WJOchman/modular_hpc/research_folder/Images/PXE.jpg

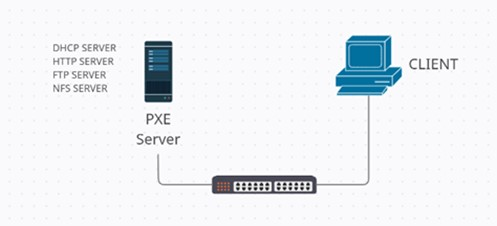
research_folder/Images/PXE.jpg
