WJOchman/modular_hpc/research_folder/Images/squeue.jpeg

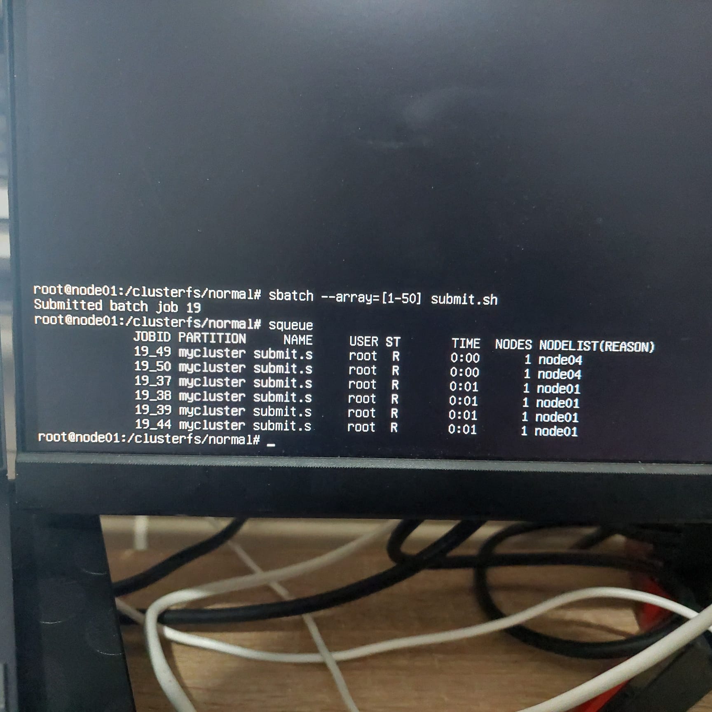
research_folder/Images/squeue.jpeg
