WJOchman/modular_hpc/hpc_case_design/laser_cutting/dxf_files/outer_shelf/outer_layer_b.dxf

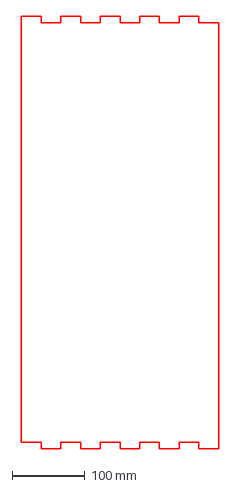
[picture p39: CAD file, 2024-04-06]
hpc_case_design/laser_cutting/dxf_files/outer_shelf/outer_layer_b.dxf
270.0 x 593.0 mm
