WJOchman/modular_hpc/hpc_case_design/3d_printing/stl_files/general-shelf/shelf_handle.stl

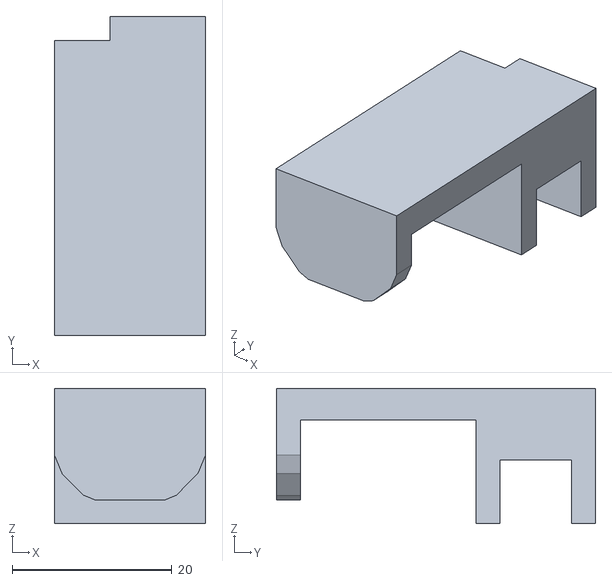
[picture p40: CAD file, 2024-04-06]
hpc_case_design/3d_printing/stl_files/general-shelf/shelf_handle.stl
18.9 x 40.0 x 17.0
