WJOchman/modular_hpc/hpc_case_design/laser_cutting/dxf_files/inner_shelf/inner_shelf_top.dxf

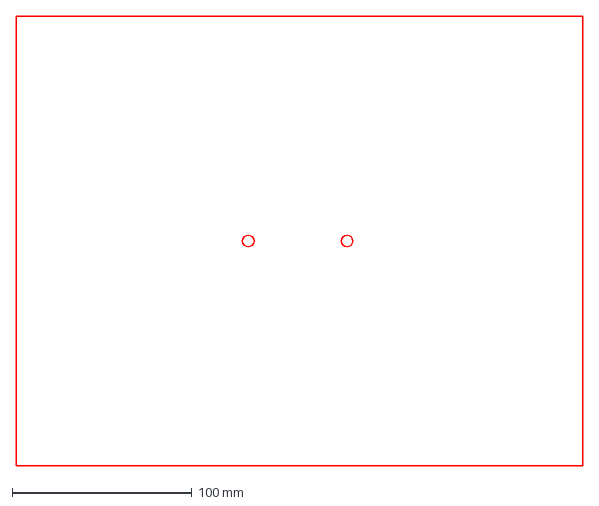
[picture p42: CAD file, 2024-04-06]
hpc_case_design/laser_cutting/dxf_files/inner_shelf/inner_shelf_top.dxf
315.0 x 250.0 mm
