WJOchman/modular_hpc/hpc_case_design/3d_printing/stl_files/general-shelf/truss.stl

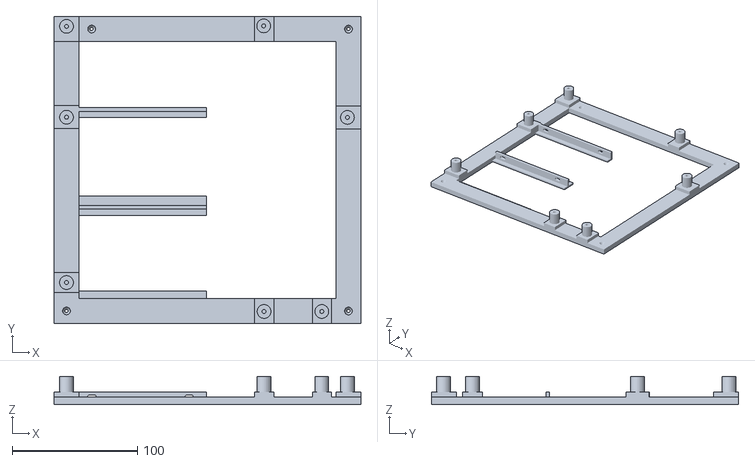
[picture p43: CAD file, 2024-04-06]
hpc_case_design/3d_printing/stl_files/general-shelf/truss.stl
244.8 x 244.8 x 22.4
