WJOchman/modular_hpc/hpc_case_design/laser_cutting/dxf_files/inner_shelf/inner_head_shelf_back.dxf

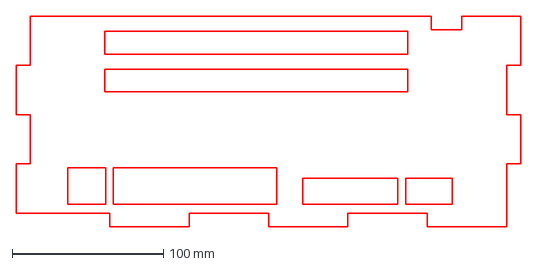
[picture p45: CAD file, 2024-04-06]
hpc_case_design/laser_cutting/dxf_files/inner_shelf/inner_head_shelf_back.dxf
333.0 x 139.0 mm
