WJOchman/modular_hpc/hpc_case_design/3d_printing/stl_files/general-shelf/truss_hole_test.stl

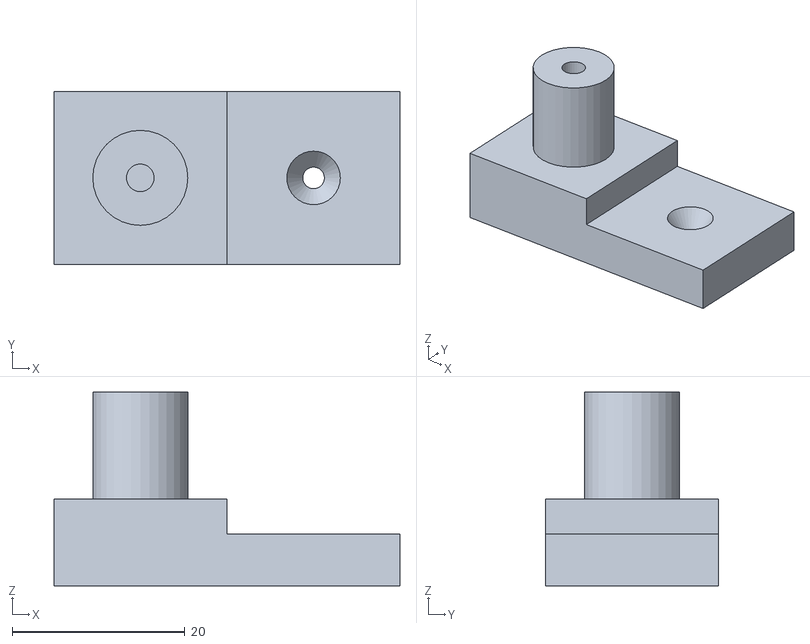
[picture p46: CAD file, 2024-04-06]
hpc_case_design/3d_printing/stl_files/general-shelf/truss_hole_test.stl
40.0 x 20.0 x 22.4
