WJOchman/modular_hpc/hpc_case_design/laser_cutting/dxf_files/inner_shelf/inner_shelf_left.dxf

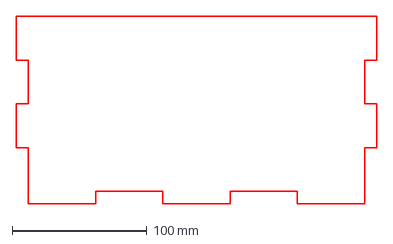
[picture p47: CAD file, 2024-04-06]
hpc_case_design/laser_cutting/dxf_files/inner_shelf/inner_shelf_left.dxf
268.0 x 139.0 mm
