WJOchman/modular_hpc/hpc_case_design/3d_printing/stl_files/general-shelf/top_wall_handle.stl

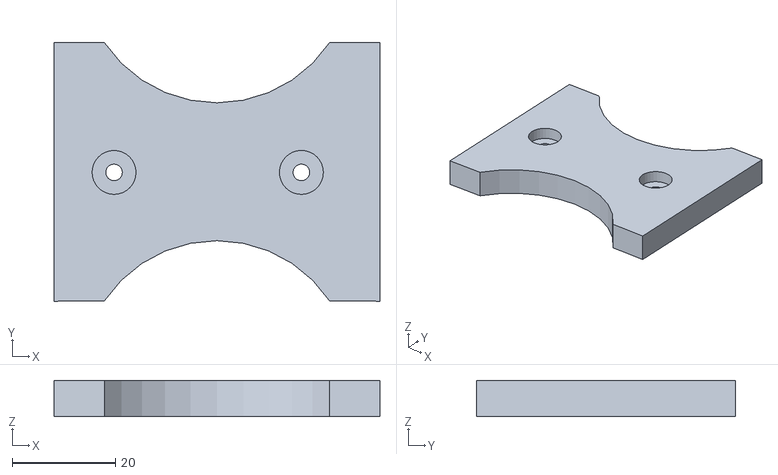
[picture p48: CAD file, 2024-04-06]
hpc_case_design/3d_printing/stl_files/general-shelf/top_wall_handle.stl
63.0 x 50.0 x 7.00
