WJOchman/modular_hpc/hpc_case_design/3d_printing/cad_files/renders/render_8.png

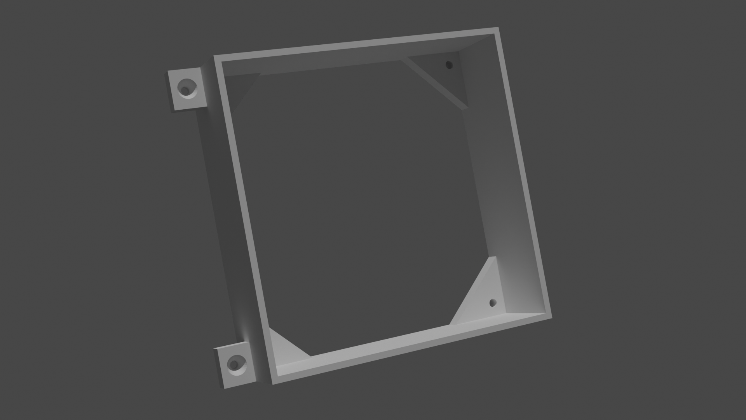
hpc_case_design/3d_printing/cad_files/renders/render_8.png
